pelrun/cpc-schematics/docs/new-fcu.png

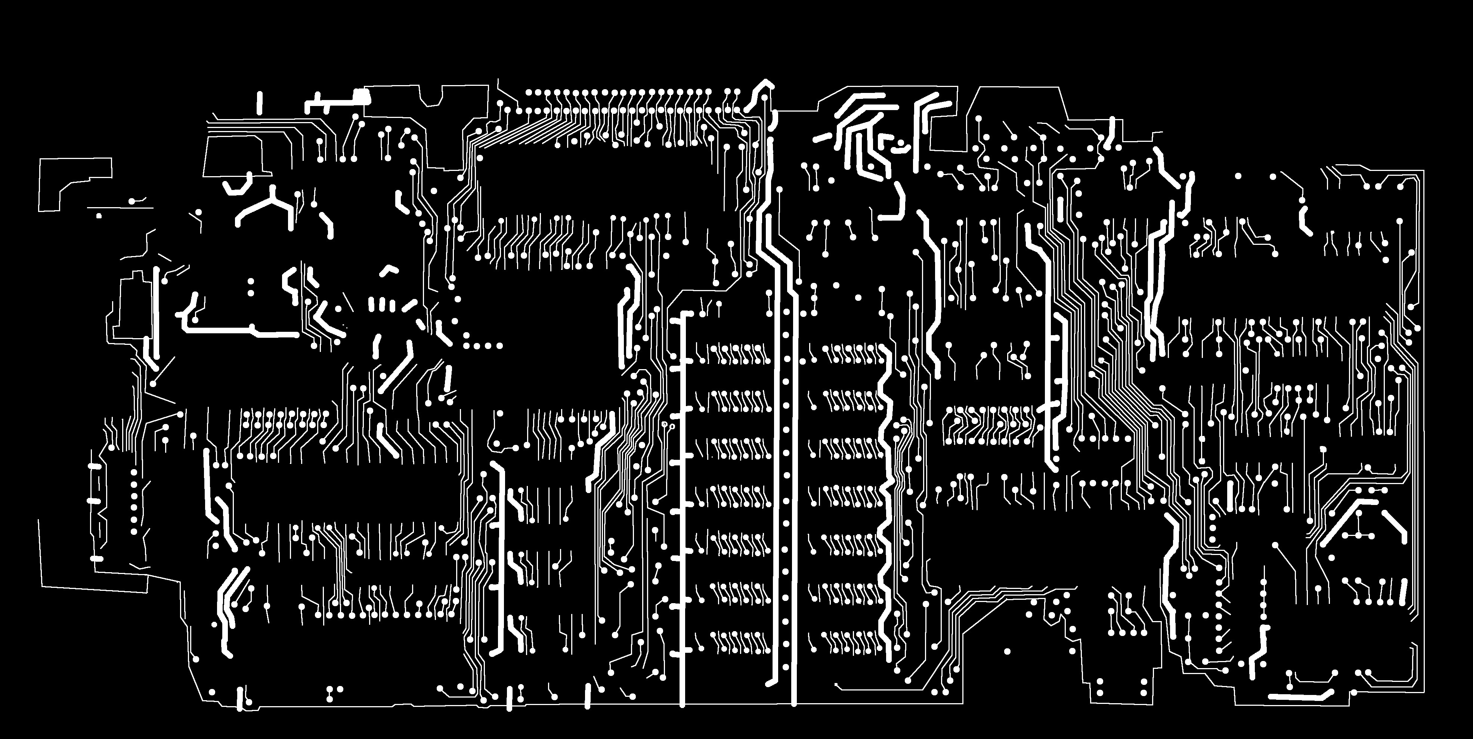
docs/new-fcu.png
