pelrun/cpc-schematics/cpc6128/disc-ver2.kicad_sch

## KiCad design cpc6128/disc-ver2.kicad_sch (2025-07-12)

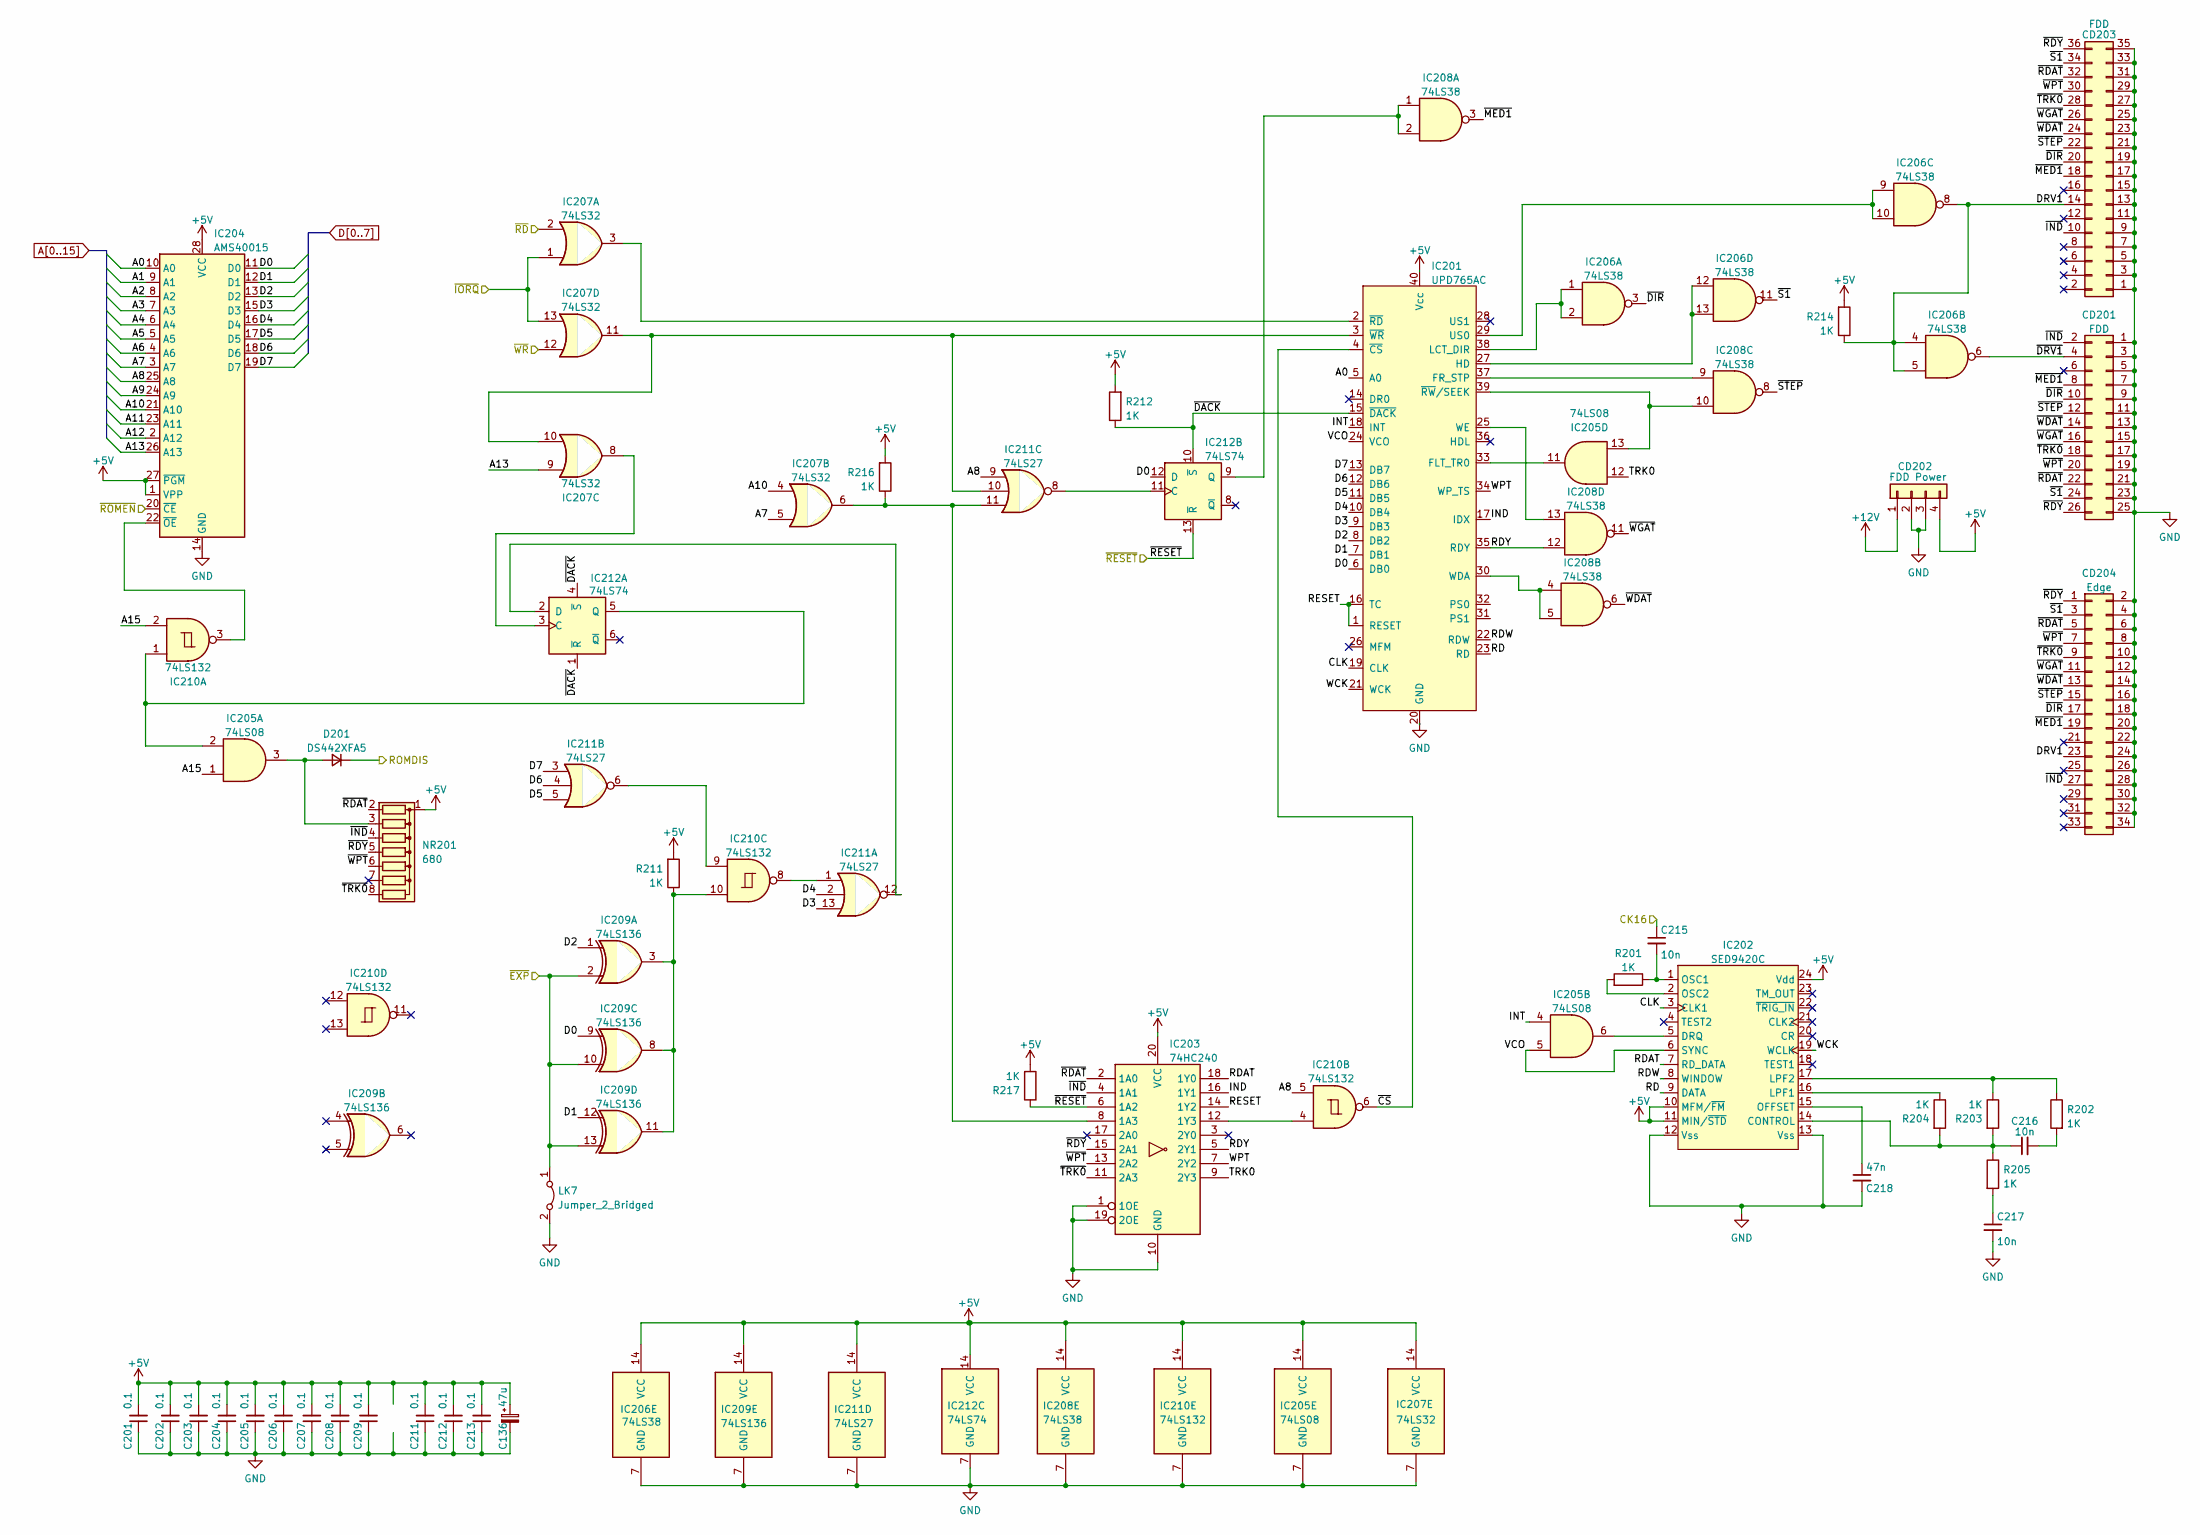
[picture p20: schematic disc-ver2.kicad_sch]

Parts:
C136: 47u; CP_Radial_D4.0mm_P5.00mm
C201, C202, C203, C204, C205, C206, C207, C208, C209, C211, C212, C213: 0.1; C_Disc_D4.3mm_W1.9mm_P5.00mm
C215, C216, C217: 10n; C_Rect_L7.0mm_W2.0mm_P5.00mm
C218: 47n; C_Rect_L7.0mm_W2.0mm_P5.00mm
CD201: FDD; IDC-Header_2x13_P2.54mm_Vertical
CD202: FDD Power; FDD_Power
CD203: FDD; 36-PIN-CENTRONICS
CD204: Edge; Edge_Conn_2x17
D201: DS442XFA5; D_DO-35_SOD27_P10.16mm_Horizontal
IC201: UPD765AC; DIP-40_W15.24mm
IC202: SED9420C; DIP-24_W15.24mm
IC203: 74HC240; DIP-20_W7.62mm
IC204: AMS40015; DIP-28_W15.24mm
IC205: 74LS08; DIP-14_W7.62mm
IC206, IC208: 74LS38; DIP-14_W7.62mm
IC207: 74LS32; DIP-14_W7.62mm
IC209: 74LS136; DIP-14_W7.62mm
IC210: 74LS132; DIP-14_W7.62mm
IC211: 74LS27; DIP-14_W7.62mm
IC212: 74LS74; DIP-14_W7.62mm
LK7: Jumper_2_Bridged; LINK
NR201: 680; R_Array_SIP8
R201, R202, R203, R204, R205, R211, R212, R214, R216, R217: 1K; R_Axial_DIN0207_L6.3mm_D2.5mm_P10.16mm_Horizontal

Connections:
+5V: C136.1, C201.2, C202.2, C203.2, C204.2, C205.2, C206.2, C207.2, C208.2, C209.2, C211.2, C212.2, C213.2, CD202.4, IC201.40 (Vcc), IC202.10 (MFM/~FM), IC202.11 (MIN/~STD), IC202.24 (Vdd), IC203.20 (VCC), IC204.1 (VPP), IC204.27 (~PGM), IC204.28 (VCC), IC205.14 (VCC), IC206.14 (VCC), IC207.14 (VCC), IC208.14 (VCC), IC209.14 (VCC), IC210.14 (VCC), IC211.14 (VCC), IC212.14 (VCC), NR201.1 (common), R211.2, R212.2, R214.2, R216.2, R217.2
+12V: CD202.1
A0: IC201.5 (A0), IC204.10 (A0)
A1: IC204.9 (A1)
A2: IC204.8 (A2)
A3: IC204.7 (A3)
A4: IC204.6 (A4)
A5: IC204.5 (A5)
A6: IC204.4 (A6)
A7: IC204.3 (A7), IC207.5
A8: IC204.25 (A8), IC210.5, IC211.9
A9: IC204.24 (A9)
A10: IC204.21 (A10), IC207.4
A11: IC204.23 (A11)
A12: IC204.2 (A12)
A13: IC204.26 (A13), IC207.9
A15: IC205.1, IC210.2
CK16: C215.1
CLK: IC201.19 (CLK), IC202.3 (CLK1)
D0: IC201.6 (DB0), IC204.11 (D0), IC209.9, IC212.12 (D)
D1: IC201.7 (DB1), IC204.12 (D1), IC209.12
D2: IC201.8 (DB2), IC204.13 (D2), IC209.1
D3: IC201.9 (DB3), IC204.15 (D3), IC211.13
D4: IC201.10 (DB4), IC204.16 (D4), IC211.2
D5: IC201.11 (DB5), IC204.17 (D5), IC211.5
D6: IC201.12 (DB6), IC204.18 (D6), IC211.4
D7: IC201.13 (DB7), IC204.19 (D7), IC211.3
DRV1: CD203.14, CD204.23, IC206.4, IC206.5, IC206.8, R214.1
GND: C136.2, C201.1, C202.1, C203.1, C204.1, C205.1, C206.1, C207.1, C208.1, C209.1, C211.1, C212.1, C213.1, C217.2, C218.2, CD201.1, CD201.3, CD201.5, CD201.7, CD201.9, CD201.11, CD201.13, CD201.15, CD201.17, CD201.19, CD201.21, CD201.23, CD201.25, CD202.2, CD202.3, CD203.1, CD203.3, CD203.5, CD203.7, CD203.9, CD203.11, CD203.13, CD203.15, CD203.17, CD203.19, CD203.21, CD203.23, CD203.25, CD203.27, CD203.29, CD203.31, CD203.33, CD203.35, CD204.2, CD204.4, CD204.6, CD204.8, CD204.10, CD204.12, CD204.14, CD204.16, CD204.18, CD204.20, CD204.22, CD204.24, CD204.26, CD204.28, CD204.30, CD204.32, CD204.34, IC201.20 (GND), IC202.12 (Vss), IC202.13 (Vss), IC203.1 (1OE), IC203.10 (GND), IC203.19 (2OE), IC204.14 (GND), IC205.7 (GND), IC206.7 (GND), IC207.7 (GND), IC208.7 (GND), IC209.7 (GND), IC210.7 (GND), IC211.7 (GND), IC212.7 (GND), LK7.2 (B)
IND: IC201.17 (IDX), IC203.16 (1Y1)
INT: IC201.18 (INT), IC205.4
unnamed: C215.2, IC202.1 (OSC1), R201.1
unnamed: C216.1, IC202.14 (CONTROL), R203.2, R204.2, R205.1
unnamed: C216.2, R202.2
unnamed: C217.1, R205.2
unnamed: C218.1, IC202.15 (OFFSET)
unnamed: D201.2 (A), IC205.3, NR201.3 (R2)
unnamed: IC201.2 (~RD), IC207.3
unnamed: IC201.3 (~WR), IC207.10, IC207.11, IC211.10
unnamed: IC201.25 (WE), IC208.13
unnamed: IC201.27 (HD), IC206.12, IC206.13
unnamed: IC201.29 (US0), IC206.9, IC206.10
unnamed: IC201.30 (WDA), IC208.4, IC208.5
unnamed: IC201.33 (FLT_TR0), IC205.11
unnamed: IC201.37 (FR_STP), IC208.9
unnamed: IC201.38 (LCT_DIR), IC206.1, IC206.2
unnamed: IC201.39 (~RW/SEEK), IC205.13, IC208.10
unnamed: IC202.2 (OSC2), R201.2
unnamed: IC202.5 (DRQ), IC205.6
unnamed: IC202.16 (LPF1), R204.1
unnamed: IC202.17 (LPF2), R202.1, R203.1
unnamed: IC203.8 (1A3), IC207.6, IC211.11, R216.1
unnamed: IC203.12 (1Y3), IC210.4
unnamed: IC204.22 (~OE), IC210.3
unnamed: IC205.2, IC210.1, IC212.5 (Q)
unnamed: IC207.8, IC212.3 (C)
unnamed: IC208.1, IC208.2, IC212.9 (Q)
unnamed: IC209.3, IC209.8, IC209.11, IC210.10, R211.1
unnamed: IC210.8, IC211.1
unnamed: IC210.9, IC211.6
unnamed: IC211.8, IC212.11 (C)
unnamed: IC211.12, IC212.2 (D)
RD: IC201.23 (RD), IC202.9 (DATA)
RDAT: IC202.7 (RD_DATA), IC203.18 (1Y0)
RDW: IC201.22 (RDW), IC202.8 (WINDOW)
RDY: IC201.35 (RDY), IC203.5 (2Y1), IC208.12
RESET: IC201.1 (RESET), IC201.16 (TC), IC203.14 (1Y2)
ROMDIS: D201.1 (K)
TRK0: IC203.9 (2Y3), IC205.12
VCO: IC201.24 (VCO), IC202.6 (SYNC), IC205.5
WCK: IC201.21 (WCK), IC202.19 (WCLK)
WPT: IC201.34 (WP_TS), IC203.7 (2Y2)
~CS: IC201.4 (~CS), IC210.6
~DACK: IC201.15 (~DACK), IC212.1 (~R), IC212.4 (~S), IC212.10 (~S), R212.1
~DIR: CD201.10, CD203.20, CD204.17, IC206.3
~DRV1: CD201.4, IC206.6
~EXP: IC209.2, IC209.10, IC209.13, LK7.1 (A)
~IND: CD201.2, CD203.10, CD204.27, IC203.4 (1A1), NR201.4 (R3)
~IORQ: IC207.1, IC207.13
~MED1: CD201.8, CD203.18, CD204.19, IC208.3
~RDAT: CD201.22, CD203.32, CD204.5, IC203.2 (1A0), NR201.2 (R1)
~RDY: CD201.26, CD203.36, CD204.1, IC203.15 (2A1), NR201.5 (R4)
~RD: IC207.2
~RESET: IC203.6 (1A2), IC212.13 (~R), R217.1
~ROMEN: IC204.20 (~CE)
~S1: CD201.24, CD203.34, CD204.3, IC206.11
~STEP: CD201.12, CD203.22, CD204.15, IC208.8
~TRK0: CD201.18, CD203.28, CD204.9, IC203.11 (2A3), NR201.8 (R7)
~WDAT: CD201.14, CD203.24, CD204.13, IC208.6
~WGAT: CD201.16, CD203.26, CD204.11, IC208.11
~WPT: CD201.20, CD203.30, CD204.7, IC203.13 (2A2), NR201.6 (R5)
~WR: IC207.12
