pelrun/cpc-schematics/cpc6128/mc0020x.kicad_sch

## KiCad design cpc6128/mc0020x.kicad_sch (2025-07-12)

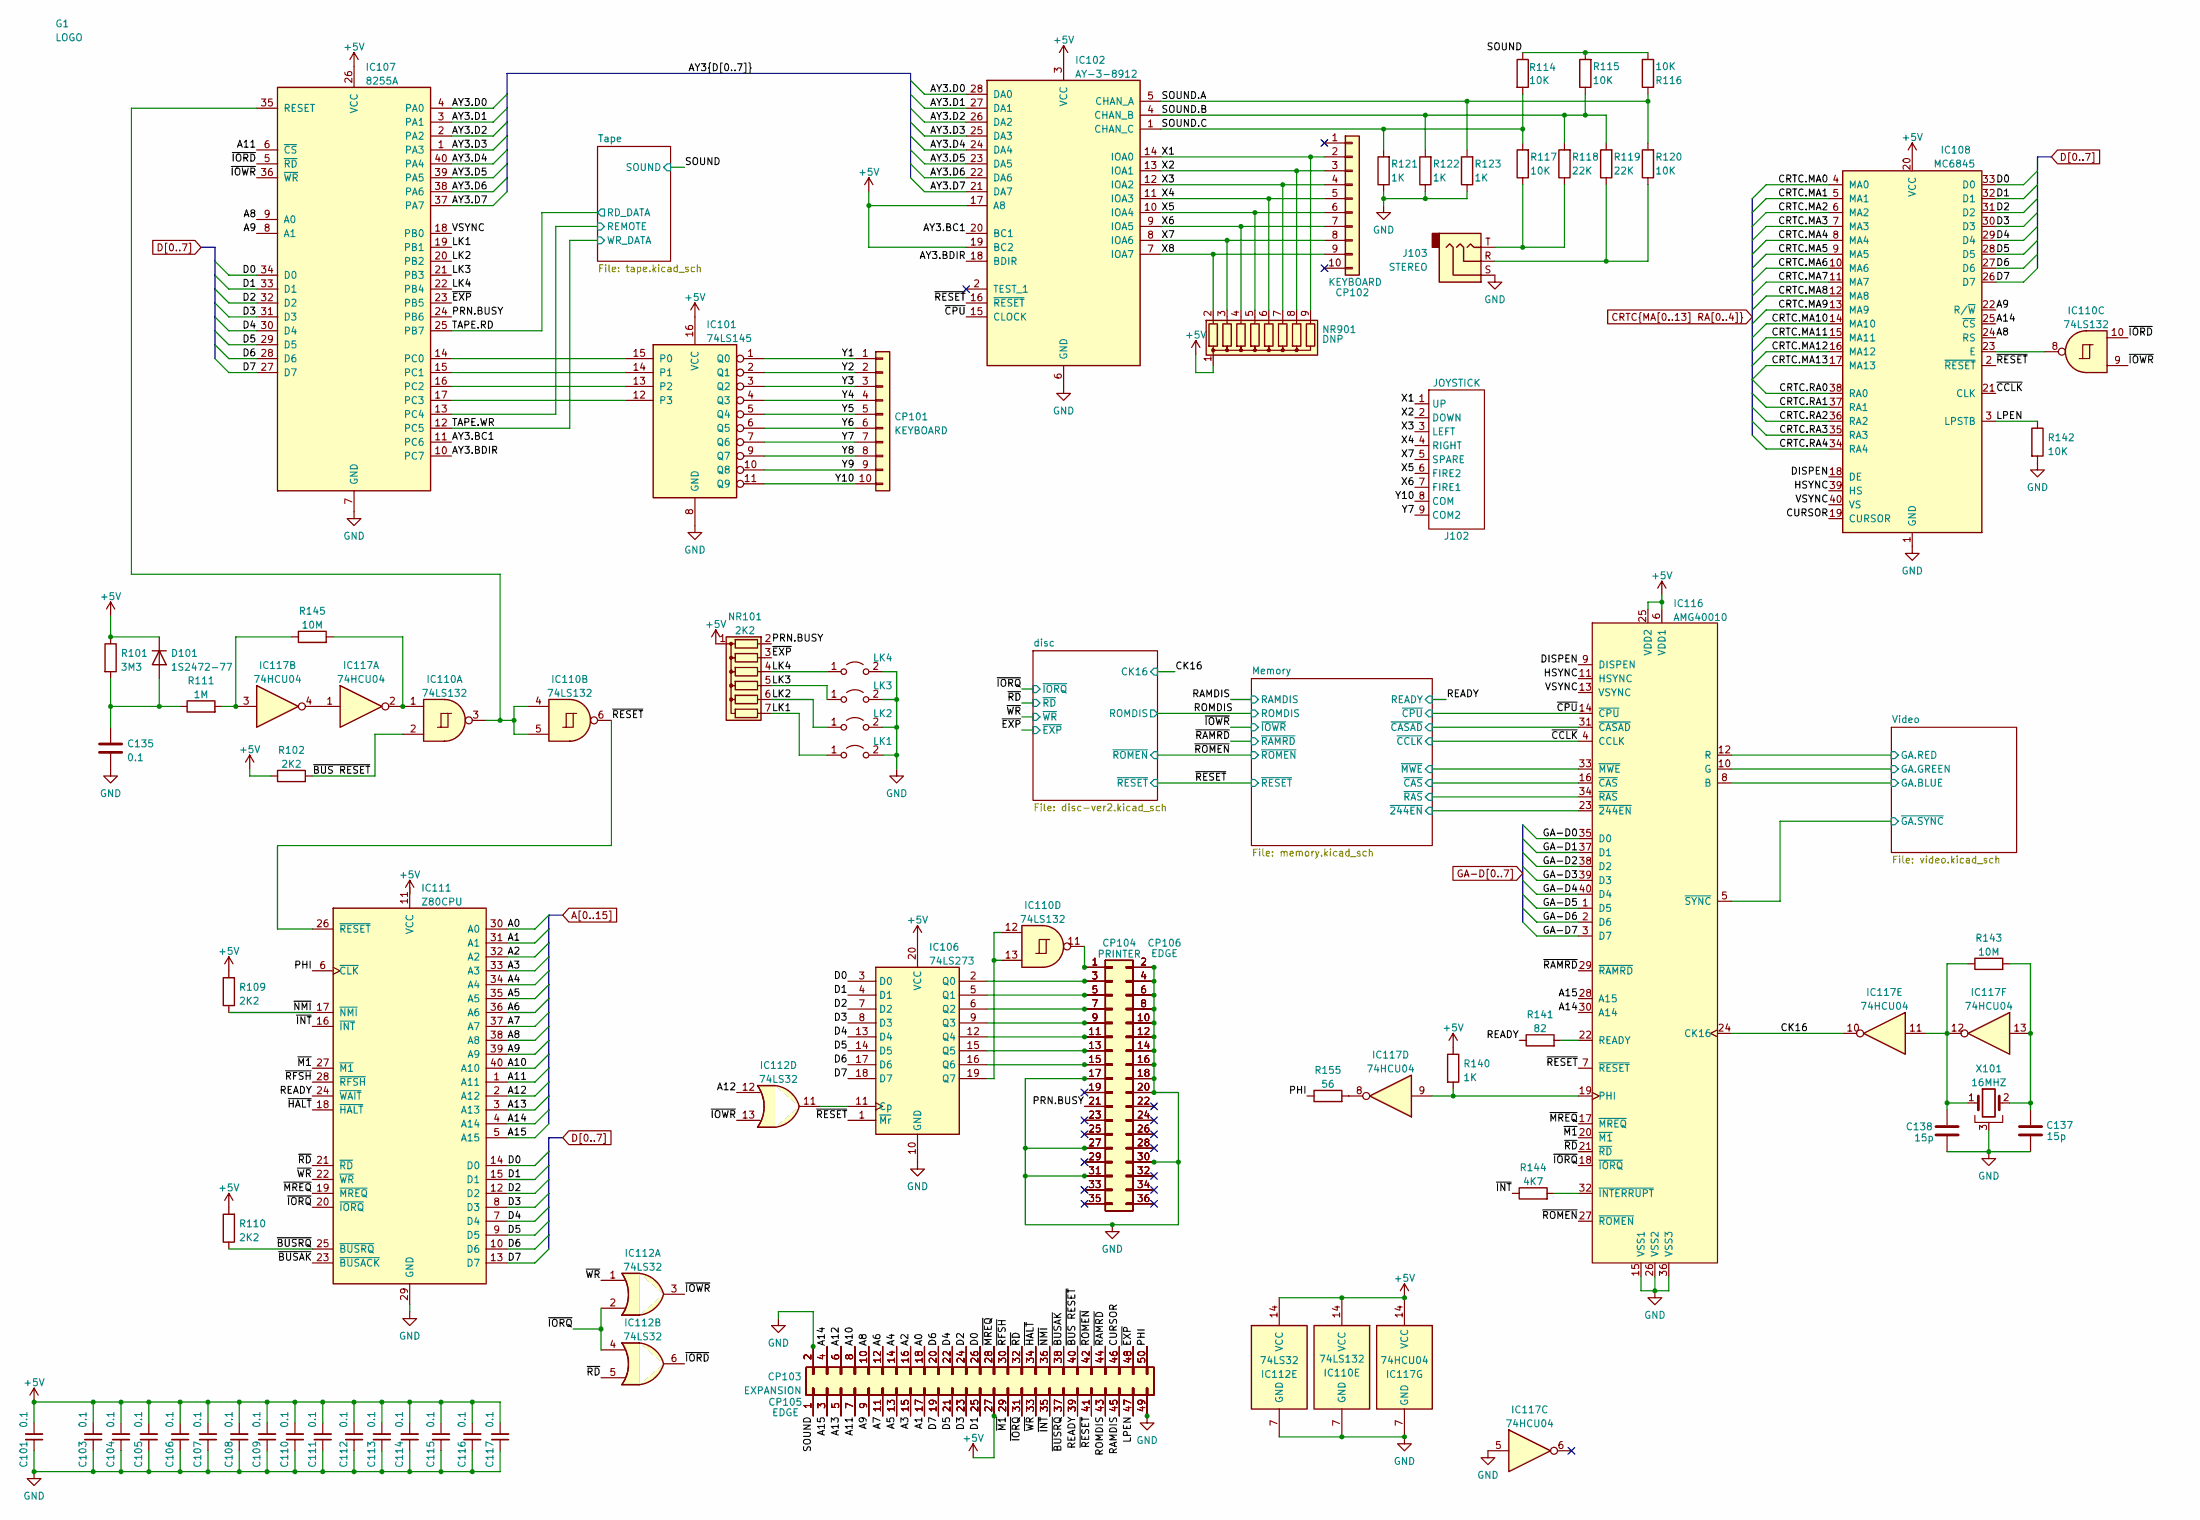
[picture p21: schematic mc0020x.kicad_sch]

Parts:
C101, C103, C104, C105, C106, C107, C108, C109, C110, C111, C112, C113, C114, C115, C116, C117, C135: 0.1; C_Disc_D4.3mm_W1.9mm_P5.00mm
C137, C138: 15p; C_Disc_D4.3mm_W1.9mm_P5.00mm
CP101, CP102: KEYBOARD; HBLB10S-5J
CP103: EXPANSION; 50-PIN-CENTRONICS
CP104: PRINTER; 36-PIN-CENTRONICS
CP105: EDGE; Edge_Conn_2x25
CP106: EDGE; Edge_Conn_2x17
D101: 1S2472-77; D_DO-35_SOD27_P10.16mm_Horizontal
G1: LOGO
IC101: 74LS145; DIP-16_W7.62mm
IC102: AY-3-8912; DIP-28_W15.24mm
IC106: 74LS273; DIP-20_W7.62mm
IC107: 8255A; DIP-40_W15.24mm
IC108: MC6845; DIP-40_W15.24mm
IC110: 74LS132; DIP-14_W7.62mm
IC111: Z80CPU; DIP-40_W15.24mm
IC112: 74LS32; DIP-14_W7.62mm
IC116: AMG40010; DIP-40_W15.24mm_Socket
IC117: 74HCU04; DIP-14_W7.62mm
J102: JOYSTICK; DSUB-9_Male_Horizontal_P2.77x2.54mm_EdgePinOffset9.40mm
J103: STEREO; HSJ1061-0104409
LK1, LK2, LK3, LK4: Jumper_2_Open; LINK
NR101: 2K2; R_Array_SIP7
NR901: DNP; R_Array_SIP9
R101: 3M3; R_Axial_DIN0207_L6.3mm_D2.5mm_P10.16mm_Horizontal
R102, R109, R110: 2K2; R_Axial_DIN0207_L6.3mm_D2.5mm_P10.16mm_Horizontal
R111: 1M; R_Axial_DIN0207_L6.3mm_D2.5mm_P10.16mm_Horizontal
R114, R115, R116, R117, R120, R142: 10K; R_Axial_DIN0207_L6.3mm_D2.5mm_P10.16mm_Horizontal
R118, R119: 22K; R_Axial_DIN0207_L6.3mm_D2.5mm_P10.16mm_Horizontal
R121, R122, R123, R140: 1K; R_Axial_DIN0207_L6.3mm_D2.5mm_P10.16mm_Horizontal
R141: 82; R_Axial_DIN0207_L6.3mm_D2.5mm_P10.16mm_Horizontal
R143, R145: 10M; R_Axial_DIN0207_L6.3mm_D2.5mm_P10.16mm_Horizontal
R144: 4K7; R_Axial_DIN0207_L6.3mm_D2.5mm_P10.16mm_Horizontal
R155: 56; R_Axial_DIN0207_L6.3mm_D2.5mm_P10.16mm_Horizontal
X101: 16MHZ; Crystal_HC18-U_Horizontal_1EP_style1

Connections:
+5V: C101.2, C103.2, C104.2, C105.2, C106.2, C107.2, C108.2, C109.2, C110.2, C111.2, C112.2, C113.2, C114.2, C115.2, C116.2, C117.2, CP103.27, CP105.27, D101.1 (K), IC101.16 (VCC), IC102.3 (VCC), IC102.17 (A8), IC102.19 (BC2), IC106.20 (VCC), IC107.26 (VCC), IC108.20 (VCC), IC110.14 (VCC), IC111.11 (VCC), IC112.14 (VCC), IC116.6 (VDD1), IC116.25 (VDD2), IC117.14 (VCC), NR101.1 (common), NR901.1 (common), R101.1, R102.1, R109.2, R110.2, R140.1
A0: CP103.18, CP105.18, IC111.30 (A0)
A1: CP103.17, CP105.17, IC111.31 (A1)
A2: CP103.16, CP105.16, IC111.32 (A2)
A3: CP103.15, CP105.15, IC111.33 (A3)
A4: CP103.14, CP105.14, IC111.34 (A4)
A5: CP103.13, CP105.13, IC111.35 (A5)
A6: CP103.12, CP105.12, IC111.36 (A6)
A7: CP103.11, CP105.11, IC111.37 (A7)
A8: CP103.10, CP105.10, IC107.9 (A0), IC108.24 (RS), IC111.38 (A8)
A9: CP103.9, CP105.9, IC107.8 (A1), IC108.22 (R/~W), IC111.39 (A9)
A10: CP103.8, CP105.8, IC111.40 (A10)
A11: CP103.7, CP105.7, IC107.6 (~CS), IC111.1 (A11)
A12: CP103.6, CP105.6, IC111.2 (A12), IC112.12
A13: CP103.5, CP105.5, IC111.3 (A13)
A14: CP103.4, CP105.4, IC108.25 (~CS), IC111.4 (A14), IC116.30 (A14)
A15: CP103.3, CP105.3, IC111.5 (A15), IC116.28 (A15)
AY3.BC1: IC102.20 (BC1), IC107.11 (PC6)
AY3.BDIR: IC102.18 (BDIR), IC107.10 (PC7)
AY3.D0: IC102.28 (DA0), IC107.4 (PA0)
AY3.D1: IC102.27 (DA1), IC107.3 (PA1)
AY3.D2: IC102.26 (DA2), IC107.2 (PA2)
AY3.D3: IC102.25 (DA3), IC107.1 (PA3)
AY3.D4: IC102.24 (DA4), IC107.40 (PA4)
AY3.D5: IC102.23 (DA5), IC107.39 (PA5)
AY3.D6: IC102.22 (DA6), IC107.38 (PA6)
AY3.D7: IC102.21 (DA7), IC107.37 (PA7)
CK16: IC116.24 (CK16), IC117.10
CRTC.MA0: IC108.4 (MA0)
CRTC.MA1: IC108.5 (MA1)
CRTC.MA2: IC108.6 (MA2)
CRTC.MA3: IC108.7 (MA3)
CRTC.MA4: IC108.8 (MA4)
CRTC.MA5: IC108.9 (MA5)
CRTC.MA6: IC108.10 (MA6)
CRTC.MA7: IC108.11 (MA7)
CRTC.MA8: IC108.12 (MA8)
CRTC.MA9: IC108.13 (MA9)
CRTC.MA10: IC108.14 (MA10)
CRTC.MA11: IC108.15 (MA11)
CRTC.MA12: IC108.16 (MA12)
CRTC.MA13: IC108.17 (MA13)
CRTC.RA0: IC108.38 (RA0)
CRTC.RA1: IC108.37 (RA1)
CRTC.RA2: IC108.36 (RA2)
CRTC.RA3: IC108.35 (RA3)
CRTC.RA4: IC108.34 (RA4)
CURSOR: CP103.46, CP105.46, IC108.19 (CURSOR)
D0: CP103.26, CP105.26, IC106.3 (D0), IC107.34 (D0), IC108.33 (D0), IC111.14 (D0)
D1: CP103.25, CP105.25, IC106.4 (D1), IC107.33 (D1), IC108.32 (D1), IC111.15 (D1)
D2: CP103.24, CP105.24, IC106.7 (D2), IC107.32 (D2), IC108.31 (D2), IC111.12 (D2)
D3: CP103.23, CP105.23, IC106.8 (D3), IC107.31 (D3), IC108.30 (D3), IC111.8 (D3)
D4: CP103.22, CP105.22, IC106.13 (D4), IC107.30 (D4), IC108.29 (D4), IC111.7 (D4)
D5: CP103.21, CP105.21, IC106.14 (D5), IC107.29 (D5), IC108.28 (D5), IC111.9 (D5)
D6: CP103.20, CP105.20, IC106.17 (D6), IC107.28 (D6), IC108.27 (D6), IC111.10 (D6)
D7: CP103.19, CP105.19, IC106.18 (D7), IC107.27 (D7), IC108.26 (D7), IC111.13 (D7)
DISPEN: IC108.18 (DE), IC116.9 (DISPEN)
GA-D0: IC116.35 (D0)
GA-D1: IC116.37 (D1)
GA-D2: IC116.38 (D2)
GA-D3: IC116.39 (D3)
GA-D4: IC116.40 (D4)
GA-D5: IC116.1 (D5)
GA-D6: IC116.2 (D6)
GA-D7: IC116.3 (D7)
GA.BLUE: IC116.8 (B)
GA.GREEN: IC116.10 (G)
GA.RED: IC116.12 (R)
GND: C101.1, C103.1, C104.1, C105.1, C106.1, C107.1, C108.1, C109.1, C110.1, C111.1, C112.1, C113.1, C114.1, C115.1, C116.1, C117.1, C135.2, C137.1, C138.2, CP103.2, CP103.49, CP104.2, CP104.4, CP104.6, CP104.8, CP104.10, CP104.12, CP104.14, CP104.16, CP104.17, CP104.18, CP104.20, CP104.27, CP104.30, CP104.31, CP105.2, CP105.49, CP106.2, CP106.4, CP106.6, CP106.8, CP106.10, CP106.12, CP106.14, CP106.16, CP106.17, CP106.18, CP106.20, CP106.27, CP106.30, CP106.31, IC101.8 (GND), IC102.6 (GND), IC106.10 (GND), IC107.7 (GND), IC108.1 (GND), IC110.7 (GND), IC111.29 (GND), IC112.7 (GND), IC116.15 (VSS1), IC116.26 (VSS2), IC116.36 (VSS3), IC117.5, IC117.7 (GND), J103.S, LK1.2 (B), LK2.2 (B), LK3.2 (B), LK4.2 (B), R121.1, R122.1, R123.1, R142.2, X101.3
HSYNC: IC108.39 (HS), IC116.11 (HSYNC)
LK1: IC107.19 (PB1), LK1.1 (A), NR101.7 (R6)
LK2: IC107.20 (PB2), LK2.1 (A), NR101.6 (R5)
LK3: IC107.21 (PB3), LK3.1 (A), NR101.5 (R4)
LK4: IC107.22 (PB4), LK4.1 (A), NR101.4 (R3)
LPEN: CP103.47, CP105.47, IC108.3 (LPSTB), R142.1
unnamed: C135.1, D101.2 (A), R101.2, R111.1
unnamed: C137.2, IC117.13, R143.2, X101.2
unnamed: C138.1, IC117.11, IC117.12, R143.1, X101.1
unnamed: CP104.1, CP106.1, IC110.11
unnamed: CP104.3, CP106.3, IC106.2 (Q0)
unnamed: CP104.5, CP106.5, IC106.5 (Q1)
unnamed: CP104.7, CP106.7, IC106.6 (Q2)
unnamed: CP104.9, CP106.9, IC106.9 (Q3)
unnamed: CP104.11, CP106.11, IC106.12 (Q4)
unnamed: CP104.13, CP106.13, IC106.15 (Q5)
unnamed: CP104.15, CP106.15, IC106.16 (Q6)
unnamed: CP104.19, CP106.19
unnamed: CP104.22, CP106.22
unnamed: CP104.23, CP106.23
unnamed: CP104.24, CP106.24
unnamed: CP104.25, CP106.25
unnamed: CP104.26, CP106.26
unnamed: CP104.28, CP106.28
unnamed: CP104.29, CP106.29
unnamed: CP104.32, CP106.32
unnamed: CP104.33, CP106.33
unnamed: CP104.34, CP106.34
unnamed: CP104.35, CP106.35
unnamed: CP104.36, CP106.36
unnamed: IC101.12 (P3), IC107.17 (PC3)
unnamed: IC101.13 (P2), IC107.16 (PC2)
unnamed: IC101.14 (P1), IC107.15 (PC1)
unnamed: IC101.15 (P0), IC107.14 (PC0)
unnamed: IC106.11 (Cp), IC112.11
unnamed: IC106.19 (Q7), IC110.12, IC110.13
unnamed: IC107.35 (RESET), IC110.3, IC110.4, IC110.5
unnamed: IC108.23 (E), IC110.8
unnamed: IC110.1, IC117.2, R145.2
unnamed: IC116.19 (PHI), IC117.9, R140.2
unnamed: IC116.22 (READY), R141.2
unnamed: IC116.32 (~INTERRUPT), R144.2
unnamed: IC117.1, IC117.4
unnamed: IC117.3, R111.2, R145.1
unnamed: IC117.8, R155.2
unnamed: J103.R, R119.1, R120.1
unnamed: J103.T, R117.1, R118.1
PHI: CP103.50, CP105.50, IC111.6 (~CLK), R155.1
PRN.BUSY: CP104.21, CP106.21, IC107.24 (PB6), NR101.2 (R1)
RAMDIS: CP103.45, CP105.45
READY: CP103.39, CP105.39, IC111.24 (~WAIT), R141.1
REMOTE: IC107.13 (PC4)
ROMDIS: CP103.43, CP105.43
SOUND: CP103.1, CP105.1, R114.1, R115.2, R116.1
SOUND.A: IC102.5 (CHAN_A), R116.2, R120.2, R123.2
SOUND.B: IC102.4 (CHAN_B), R115.1, R118.2, R119.2, R122.2
SOUND.C: IC102.1 (CHAN_C), R114.2, R117.2, R121.2
TAPE.RD: IC107.25 (PB7)
TAPE.WR: IC107.12 (PC5)
VSYNC: IC107.18 (PB0), IC108.40 (VS), IC116.13 (VSYNC)
X1: CP102.2, IC102.14 (IOA0), J102.1 (UP), NR901.9 (R8)
X2: CP102.3, IC102.13 (IOA1), J102.2 (DOWN), NR901.8 (R7)
X3: CP102.4, IC102.12 (IOA2), J102.3 (LEFT), NR901.7 (R6)
X4: CP102.5, IC102.11 (IOA3), J102.4 (RIGHT), NR901.6 (R5)
X5: CP102.6, IC102.10 (IOA4), J102.6 (FIRE2), NR901.5 (R4)
X6: CP102.7, IC102.9 (IOA5), J102.7 (FIRE1), NR901.4 (R3)
X7: CP102.8, IC102.8 (IOA6), J102.5 (SPARE), NR901.3 (R2)
X8: CP102.9, IC102.7 (IOA7), NR901.2 (R1)
Y1: CP101.1, IC101.1 (Q0)
Y2: CP101.2, IC101.2 (Q1)
Y3: CP101.3, IC101.3 (Q2)
Y4: CP101.4, IC101.4 (Q3)
Y5: CP101.5, IC101.5 (Q4)
Y6: CP101.6, IC101.6 (Q5)
Y7: CP101.7, IC101.7 (Q6), J102.9 (COM2)
Y8: CP101.8, IC101.9 (Q7)
Y9: CP101.9, IC101.10 (Q8)
Y10: CP101.10, IC101.11 (Q9), J102.8 (COM)
~244EN: IC116.23 (~244EN)
~BUS RESET: CP103.40, CP105.40, IC110.2, R102.2
~BUSAK: CP103.38, CP105.38, IC111.23 (~BUSACK)
~BUSRQ: CP103.37, CP105.37, IC111.25 (~BUSRQ), R110.1
~CASAD: IC116.31 (~CASAD)
~CAS: IC116.16 (~CAS)
~CCLK: IC108.21 (CLK), IC116.4 (CCLK)
~CPU: IC102.15 (CLOCK), IC116.14 (~CPU)
~EXP: CP103.48, CP105.48, IC107.23 (PB5), NR101.3 (R2)
~GA.SYNC: IC116.5 (~SYNC)
~HALT: CP103.34, CP105.34, IC111.18 (~HALT)
~INT: CP103.35, CP105.35, IC111.16 (~INT), R144.1
~IORD: IC107.5 (~RD), IC110.10, IC112.6
~IORQ: CP103.31, CP105.31, IC111.20 (~IORQ), IC112.2, IC112.4, IC116.18 (~IORQ)
~IOWR: IC107.36 (~WR), IC110.9, IC112.3, IC112.13
~M1: CP103.29, CP105.29, IC111.27 (~M1), IC116.20 (~M1)
~MREQ: CP103.28, CP105.28, IC111.19 (~MREQ), IC116.17 (~MREQ)
~MWE: IC116.33 (~MWE)
~NMI: CP103.36, CP105.36, IC111.17 (~NMI), R109.1
~RAMRD: CP103.44, CP105.44, IC116.29 (~RAMRD)
~RAS: IC116.34 (~RAS)
~RD: CP103.32, CP105.32, IC111.21 (~RD), IC112.5, IC116.21 (~RD)
~RESET: CP103.41, CP105.41, IC102.16 (~RESET), IC106.1 (~Mr), IC108.2 (~RESET), IC110.6, IC111.26 (~RESET), IC116.7 (~RESET)
~RFSH: CP103.30, CP105.30, IC111.28 (~RFSH)
~ROMEN: CP103.42, CP105.42, IC116.27 (~ROMEN)
~WR: CP103.33, CP105.33, IC111.22 (~WR), IC112.1
