pelrun/cpc-schematics/cpc6128/memory.kicad_sch

## KiCad design cpc6128/memory.kicad_sch (2025-07-12)

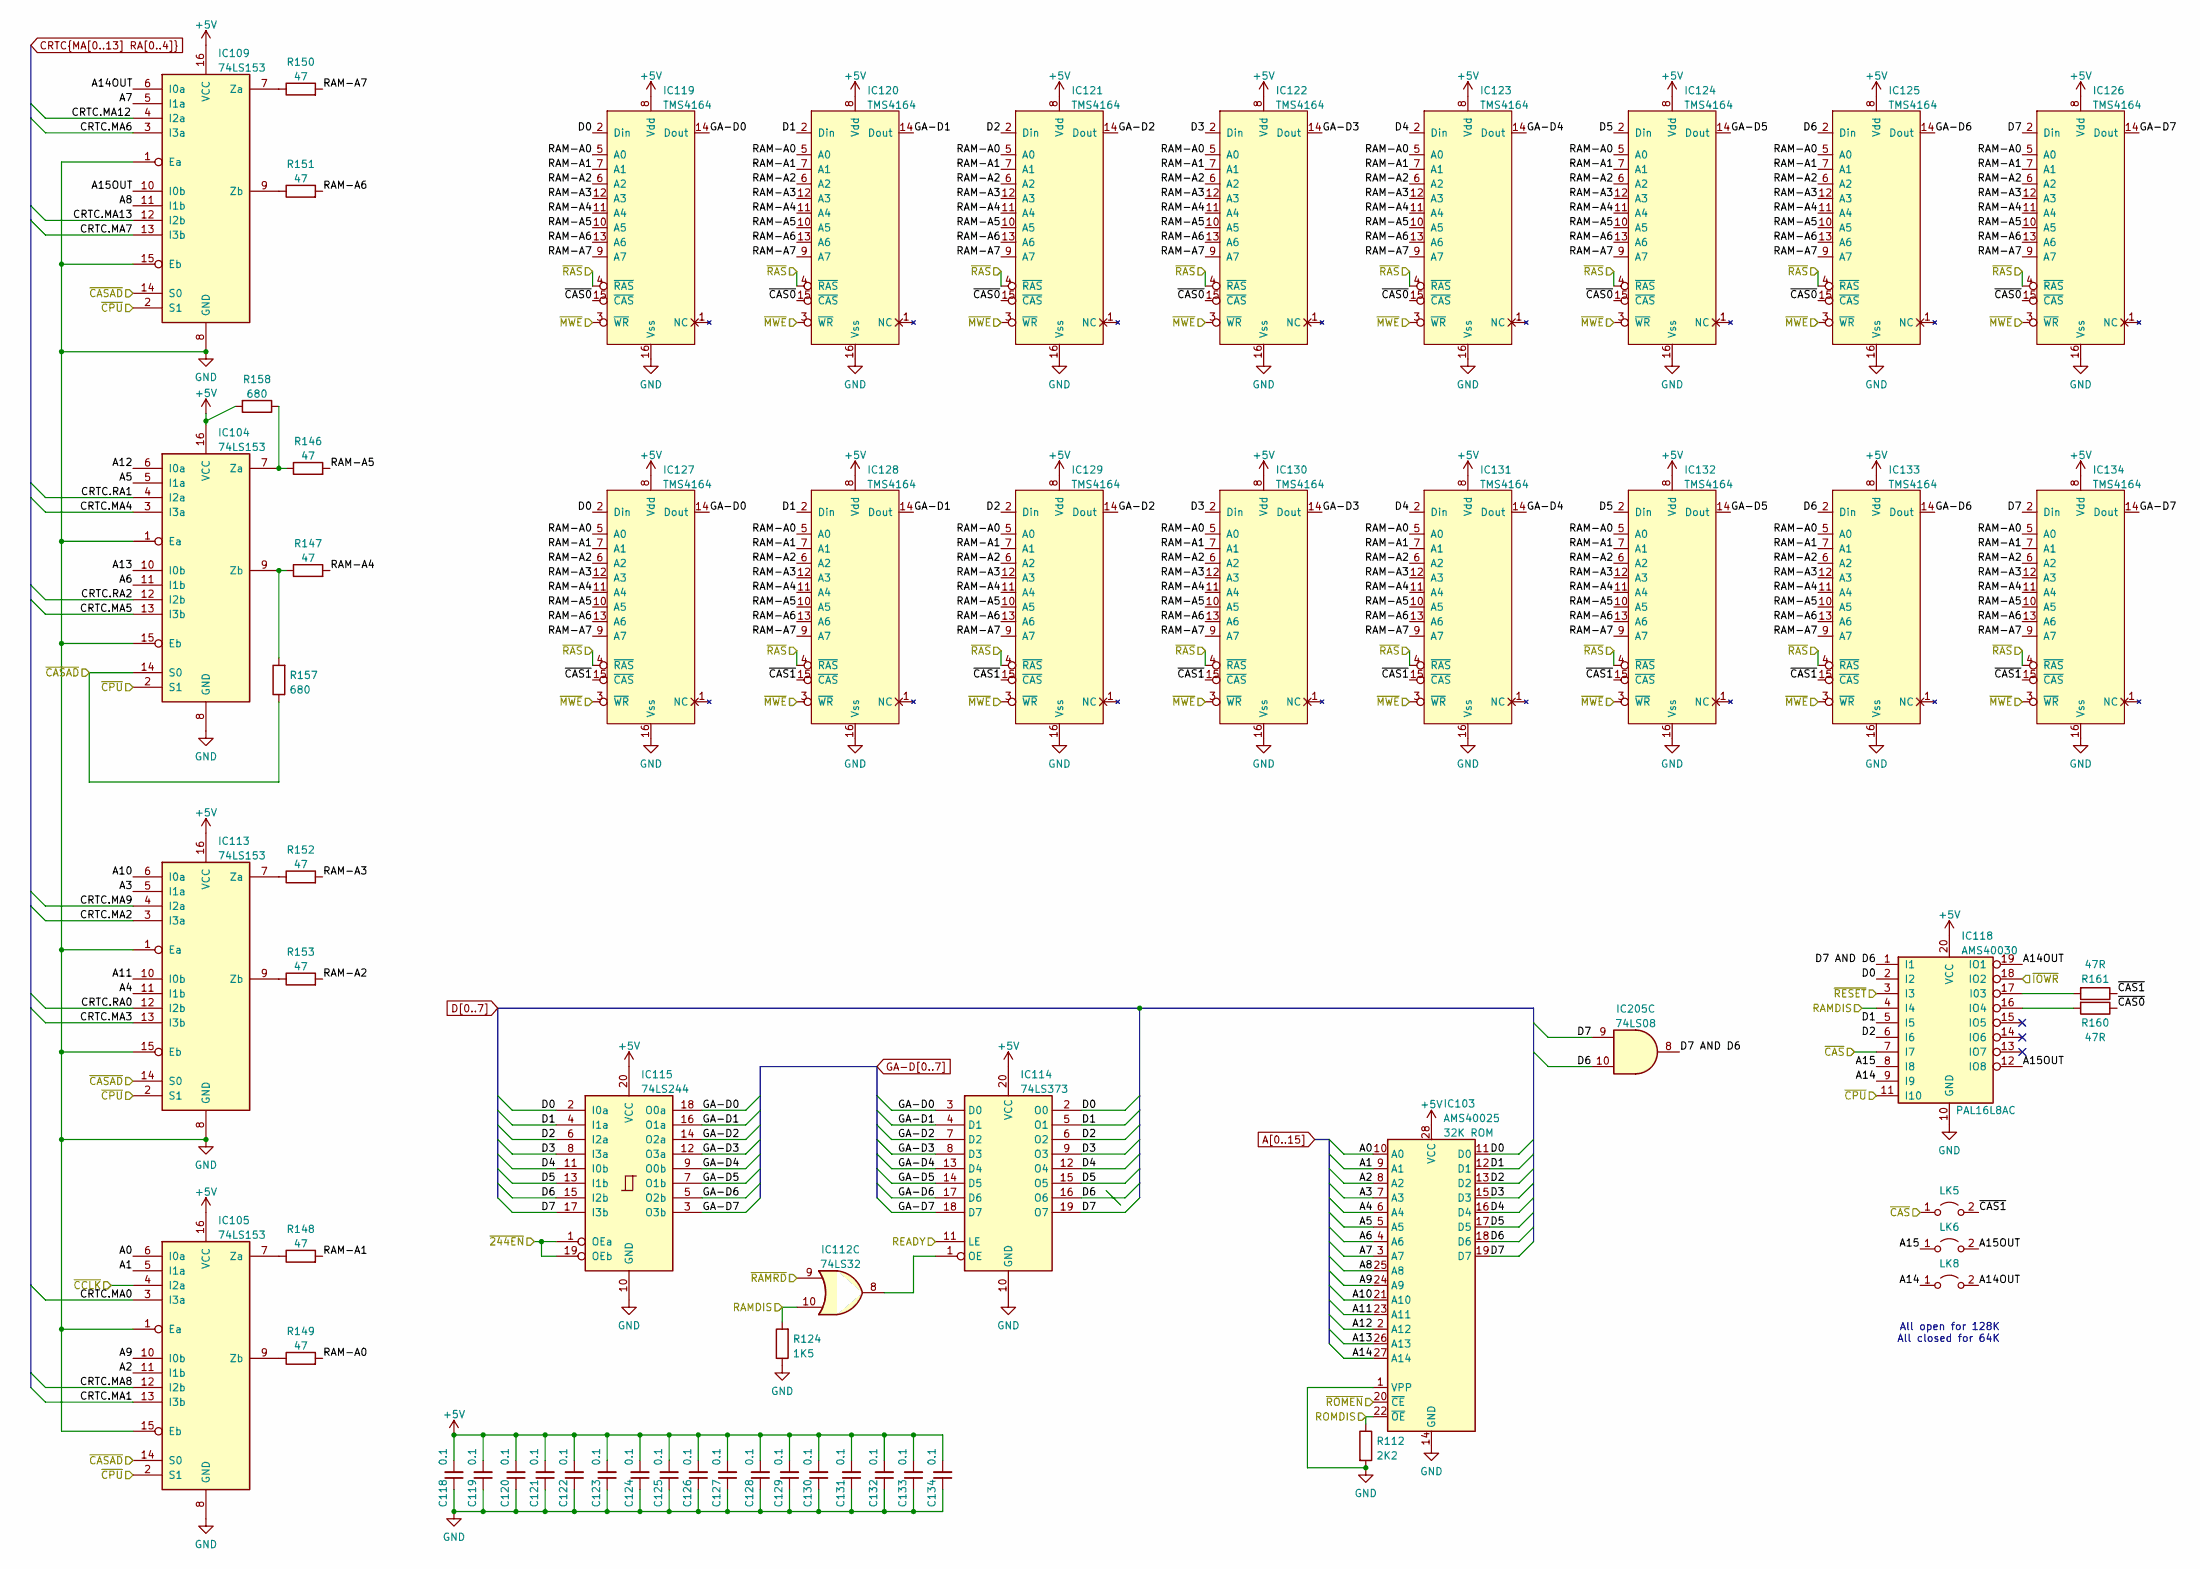
[picture p22: schematic memory.kicad_sch]

Parts:
C118, C119, C120, C121, C122, C123, C124, C125, C126, C127, C128, C129, C130, C131, C132, C133, C134: 0.1; C_Disc_D4.3mm_W1.9mm_P5.00mm
IC103: AMS40025; DIP-28_W15.24mm
IC104, IC105, IC109, IC113: 74LS153; DIP-16_W7.62mm
IC112: 74LS32; DIP-14_W7.62mm
IC114: 74LS373; DIP-20_W7.62mm
IC115: 74LS244; DIP-20_W7.62mm
IC118: AMS40030; DIP-20_W7.62mm_Socket
IC119, IC120, IC121, IC122, IC123, IC124, IC125, IC126, IC127, IC128, IC129, IC130, IC131, IC132, IC133, IC134: TMS4164; DIP-16_W7.62mm
IC205: 74LS08; DIP-14_W7.62mm
LK5, LK6, LK8: Jumper_2_Open; LINK
R112: 2K2; R_Axial_DIN0207_L6.3mm_D2.5mm_P10.16mm_Horizontal
R124: 1K5; R_Axial_DIN0207_L6.3mm_D2.5mm_P10.16mm_Horizontal
R146, R147, R148, R149, R150, R151, R152, R153: 47; R_Axial_DIN0207_L6.3mm_D2.5mm_P10.16mm_Horizontal
R157, R158: 680; R_Axial_DIN0207_L6.3mm_D2.5mm_P10.16mm_Horizontal
R160, R161: 47R; R_Axial_DIN0207_L6.3mm_D2.5mm_P10.16mm_Horizontal

Connections:
+5V: C118.2, C119.2, C120.2, C121.2, C122.2, C123.2, C124.2, C125.2, C126.2, C127.2, C128.2, C129.2, C130.2, C131.2, C132.2, C133.2, C134.2, IC103.28 (VCC), IC104.16 (VCC), IC105.16 (VCC), IC109.16 (VCC), IC113.16 (VCC), IC114.20 (VCC), IC115.20 (VCC), IC118.20 (VCC), IC119.8 (Vdd), IC120.8 (Vdd), IC121.8 (Vdd), IC122.8 (Vdd), IC123.8 (Vdd), IC124.8 (Vdd), IC125.8 (Vdd), IC126.8 (Vdd), IC127.8 (Vdd), IC128.8 (Vdd), IC129.8 (Vdd), IC130.8 (Vdd), IC131.8 (Vdd), IC132.8 (Vdd), IC133.8 (Vdd), IC134.8 (Vdd), R158.2
A0: IC103.10 (A0), IC105.6 (I0a)
A1: IC103.9 (A1), IC105.5 (I1a)
A2: IC103.8 (A2), IC105.11 (I1b)
A3: IC103.7 (A3), IC113.5 (I1a)
A4: IC103.6 (A4), IC113.11 (I1b)
A5: IC103.5 (A5), IC104.5 (I1a)
A6: IC103.4 (A6), IC104.11 (I1b)
A7: IC103.3 (A7), IC109.5 (I1a)
A8: IC103.25 (A8), IC109.11 (I1b)
A9: IC103.24 (A9), IC105.10 (I0b)
A10: IC103.21 (A10), IC113.6 (I0a)
A11: IC103.23 (A11), IC113.10 (I0b)
A12: IC103.2 (A12), IC104.6 (I0a)
A13: IC103.26 (A13), IC104.10 (I0b)
A14: IC103.27 (A14), IC118.9 (I9), LK8.1 (A)
A14OUT: IC109.6 (I0a), IC118.19 (IO1), LK8.2 (B)
A15: IC118.8 (I8), LK6.1 (A)
A15OUT: IC109.10 (I0b), IC118.12 (IO8), LK6.2 (B)
CRTC.MA0: IC105.3 (I3a)
CRTC.MA1: IC105.13 (I3b)
CRTC.MA2: IC113.3 (I3a)
CRTC.MA3: IC113.13 (I3b)
CRTC.MA4: IC104.3 (I3a)
CRTC.MA5: IC104.13 (I3b)
CRTC.MA6: IC109.3 (I3a)
CRTC.MA7: IC109.13 (I3b)
CRTC.MA8: IC105.12 (I2b)
CRTC.MA9: IC113.4 (I2a)
CRTC.MA12: IC109.4 (I2a)
CRTC.MA13: IC109.12 (I2b)
CRTC.RA0: IC113.12 (I2b)
CRTC.RA1: IC104.4 (I2a)
CRTC.RA2: IC104.12 (I2b)
D0: IC103.11 (D0), IC114.2 (O0), IC115.2 (I0a), IC118.2 (I2), IC119.2 (Din), IC127.2 (Din)
D1: IC103.12 (D1), IC114.5 (O1), IC115.4 (I1a), IC118.5 (I5), IC120.2 (Din), IC128.2 (Din)
D2: IC103.13 (D2), IC114.6 (O2), IC115.6 (I2a), IC118.6 (I6), IC121.2 (Din), IC129.2 (Din)
D3: IC103.15 (D3), IC114.9 (O3), IC115.8 (I3a), IC122.2 (Din), IC130.2 (Din)
D4: IC103.16 (D4), IC114.12 (O4), IC115.11 (I0b), IC123.2 (Din), IC131.2 (Din)
D5: IC103.17 (D5), IC114.15 (O5), IC115.13 (I1b), IC124.2 (Din), IC132.2 (Din)
D6: IC103.18 (D6), IC114.16 (O6), IC115.15 (I2b), IC125.2 (Din), IC133.2 (Din), IC205.10
D7: IC103.19 (D7), IC114.19 (O7), IC115.17 (I3b), IC126.2 (Din), IC134.2 (Din), IC205.9
D7 AND D6: IC118.1 (I1), IC205.8
GA-D0: IC114.3 (D0), IC115.18 (O0a), IC119.14 (Dout), IC127.14 (Dout)
GA-D1: IC114.4 (D1), IC115.16 (O1a), IC120.14 (Dout), IC128.14 (Dout)
GA-D2: IC114.7 (D2), IC115.14 (O2a), IC121.14 (Dout), IC129.14 (Dout)
GA-D3: IC114.8 (D3), IC115.12 (O3a), IC122.14 (Dout), IC130.14 (Dout)
GA-D4: IC114.13 (D4), IC115.9 (O0b), IC123.14 (Dout), IC131.14 (Dout)
GA-D5: IC114.14 (D5), IC115.7 (O1b), IC124.14 (Dout), IC132.14 (Dout)
GA-D6: IC114.17 (D6), IC115.5 (O2b), IC125.14 (Dout), IC133.14 (Dout)
GA-D7: IC114.18 (D7), IC115.3 (O3b), IC126.14 (Dout), IC134.14 (Dout)
GND: C118.1, C119.1, C120.1, C121.1, C122.1, C123.1, C124.1, C125.1, C126.1, C127.1, C128.1, C129.1, C130.1, C131.1, C132.1, C133.1, C134.1, IC103.1 (VPP), IC103.14 (GND), IC104.1 (Ea), IC104.8 (GND), IC104.15 (Eb), IC105.1 (Ea), IC105.8 (GND), IC105.15 (Eb), IC109.1 (Ea), IC109.8 (GND), IC109.15 (Eb), IC113.1 (Ea), IC113.8 (GND), IC113.15 (Eb), IC114.10 (GND), IC115.10 (GND), IC118.10 (GND), IC119.16 (Vss), IC120.16 (Vss), IC121.16 (Vss), IC122.16 (Vss), IC123.16 (Vss), IC124.16 (Vss), IC125.16 (Vss), IC126.16 (Vss), IC127.16 (Vss), IC128.16 (Vss), IC129.16 (Vss), IC130.16 (Vss), IC131.16 (Vss), IC132.16 (Vss), IC133.16 (Vss), IC134.16 (Vss), R112.2, R124.1
unnamed: IC104.7 (Za), R146.1, R158.1
unnamed: IC104.9 (Zb), R147.1, R157.2
unnamed: IC105.7 (Za), R148.1
unnamed: IC105.9 (Zb), R149.1
unnamed: IC109.7 (Za), R150.1
unnamed: IC109.9 (Zb), R151.1
unnamed: IC112.8, IC114.1 (OE)
unnamed: IC113.7 (Za), R152.1
unnamed: IC113.9 (Zb), R153.1
unnamed: IC118.16 (IO4), R160.2
unnamed: IC118.17 (I03), R161.2
RAM-A0: IC119.5 (A0), IC120.5 (A0), IC121.5 (A0), IC122.5 (A0), IC123.5 (A0), IC124.5 (A0), IC125.5 (A0), IC126.5 (A0), IC127.5 (A0), IC128.5 (A0), IC129.5 (A0), IC130.5 (A0), IC131.5 (A0), IC132.5 (A0), IC133.5 (A0), IC134.5 (A0), R149.2
RAM-A1: IC119.7 (A1), IC120.7 (A1), IC121.7 (A1), IC122.7 (A1), IC123.7 (A1), IC124.7 (A1), IC125.7 (A1), IC126.7 (A1), IC127.7 (A1), IC128.7 (A1), IC129.7 (A1), IC130.7 (A1), IC131.7 (A1), IC132.7 (A1), IC133.7 (A1), IC134.7 (A1), R148.2
RAM-A2: IC119.6 (A2), IC120.6 (A2), IC121.6 (A2), IC122.6 (A2), IC123.6 (A2), IC124.6 (A2), IC125.6 (A2), IC126.6 (A2), IC127.6 (A2), IC128.6 (A2), IC129.6 (A2), IC130.6 (A2), IC131.6 (A2), IC132.6 (A2), IC133.6 (A2), IC134.6 (A2), R153.2
RAM-A3: IC119.12 (A3), IC120.12 (A3), IC121.12 (A3), IC122.12 (A3), IC123.12 (A3), IC124.12 (A3), IC125.12 (A3), IC126.12 (A3), IC127.12 (A3), IC128.12 (A3), IC129.12 (A3), IC130.12 (A3), IC131.12 (A3), IC132.12 (A3), IC133.12 (A3), IC134.12 (A3), R152.2
RAM-A4: IC119.11 (A4), IC120.11 (A4), IC121.11 (A4), IC122.11 (A4), IC123.11 (A4), IC124.11 (A4), IC125.11 (A4), IC126.11 (A4), IC127.11 (A4), IC128.11 (A4), IC129.11 (A4), IC130.11 (A4), IC131.11 (A4), IC132.11 (A4), IC133.11 (A4), IC134.11 (A4), R147.2
RAM-A5: IC119.10 (A5), IC120.10 (A5), IC121.10 (A5), IC122.10 (A5), IC123.10 (A5), IC124.10 (A5), IC125.10 (A5), IC126.10 (A5), IC127.10 (A5), IC128.10 (A5), IC129.10 (A5), IC130.10 (A5), IC131.10 (A5), IC132.10 (A5), IC133.10 (A5), IC134.10 (A5), R146.2
RAM-A6: IC119.13 (A6), IC120.13 (A6), IC121.13 (A6), IC122.13 (A6), IC123.13 (A6), IC124.13 (A6), IC125.13 (A6), IC126.13 (A6), IC127.13 (A6), IC128.13 (A6), IC129.13 (A6), IC130.13 (A6), IC131.13 (A6), IC132.13 (A6), IC133.13 (A6), IC134.13 (A6), R151.2
RAM-A7: IC119.9 (A7), IC120.9 (A7), IC121.9 (A7), IC122.9 (A7), IC123.9 (A7), IC124.9 (A7), IC125.9 (A7), IC126.9 (A7), IC127.9 (A7), IC128.9 (A7), IC129.9 (A7), IC130.9 (A7), IC131.9 (A7), IC132.9 (A7), IC133.9 (A7), IC134.9 (A7), R150.2
RAMDIS: IC112.10, IC118.4 (I4), R124.2
READY: IC114.11 (LE)
ROMDIS: IC103.22 (~OE), R112.1
~244EN: IC115.1 (OEa), IC115.19 (OEb)
~CAS0: IC119.15 (~CAS), IC120.15 (~CAS), IC121.15 (~CAS), IC122.15 (~CAS), IC123.15 (~CAS), IC124.15 (~CAS), IC125.15 (~CAS), IC126.15 (~CAS), R160.1
~CAS1: IC127.15 (~CAS), IC128.15 (~CAS), IC129.15 (~CAS), IC130.15 (~CAS), IC131.15 (~CAS), IC132.15 (~CAS), IC133.15 (~CAS), IC134.15 (~CAS), LK5.2 (B), R161.1
~CASAD: IC104.14 (S0), IC105.14 (S0), IC109.14 (S0), IC113.14 (S0), R157.1
~CAS: IC118.7 (I7), LK5.1 (A)
~CCLK: IC105.4 (I2a)
~CPU: IC104.2 (S1), IC105.2 (S1), IC109.2 (S1), IC113.2 (S1), IC118.11 (I10)
~IOWR: IC118.18 (IO2)
~MWE: IC119.3 (~WR), IC120.3 (~WR), IC121.3 (~WR), IC122.3 (~WR), IC123.3 (~WR), IC124.3 (~WR), IC125.3 (~WR), IC126.3 (~WR), IC127.3 (~WR), IC128.3 (~WR), IC129.3 (~WR), IC130.3 (~WR), IC131.3 (~WR), IC132.3 (~WR), IC133.3 (~WR), IC134.3 (~WR)
~RAMRD: IC112.9
~RAS: IC119.4 (~RAS), IC120.4 (~RAS), IC121.4 (~RAS), IC122.4 (~RAS), IC123.4 (~RAS), IC124.4 (~RAS), IC125.4 (~RAS), IC126.4 (~RAS), IC127.4 (~RAS), IC128.4 (~RAS), IC129.4 (~RAS), IC130.4 (~RAS), IC131.4 (~RAS), IC132.4 (~RAS), IC133.4 (~RAS), IC134.4 (~RAS)
~RESET: IC118.3 (I3)
~ROMEN: IC103.20 (~CE)

Notes on the sheet:
All open for 128K All closed for 64K
