pelrun/cpc-schematics/cpc6128/tape.kicad_sch

## KiCad design cpc6128/tape.kicad_sch (2025-07-12)

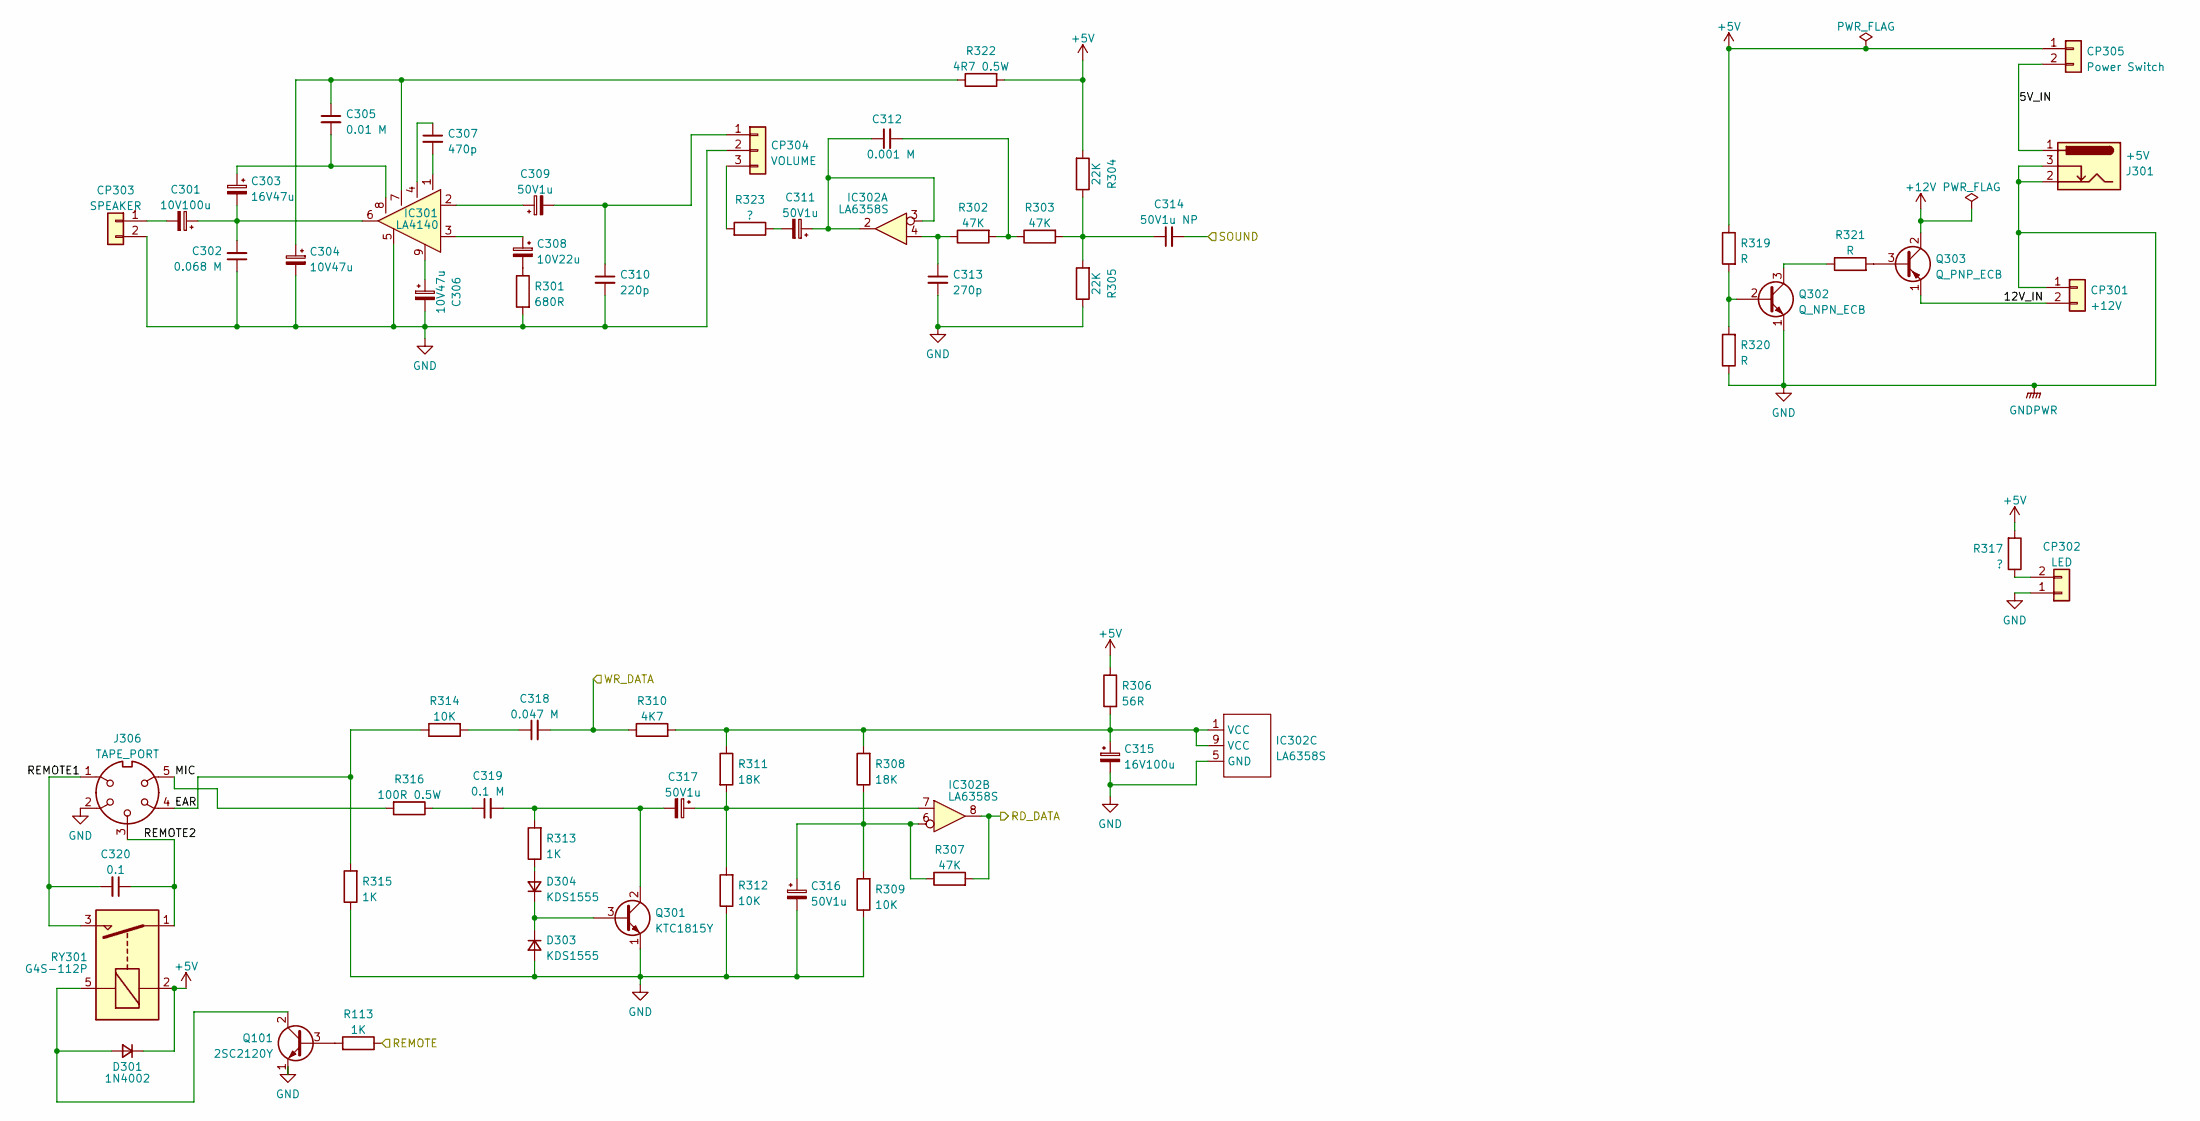
[picture p23: schematic tape.kicad_sch]

Parts:
C301: 10V100u; CP_Radial_D4.0mm_P5.00mm
C302: 0.068 M; C_Rect_L7.0mm_W2.0mm_P5.00mm
C303: 16V47u; CP_Radial_D4.0mm_P5.00mm
C304, C306: 10V47u; CP_Radial_D4.0mm_P5.00mm
C305: 0.01 M; C_Rect_L7.0mm_W2.0mm_P5.00mm
C307: 470p; C_Disc_D4.3mm_W1.9mm_P5.00mm
C308: 10V22u; CP_Radial_D4.0mm_P5.00mm
C309, C311, C316, C317: 50V1u; CP_Radial_D4.0mm_P5.00mm
C310: 220p; C_Disc_D4.3mm_W1.9mm_P5.00mm
C312: 0.001 M; C_Rect_L7.0mm_W2.0mm_P5.00mm
C313: 270p; C_Disc_D4.3mm_W1.9mm_P5.00mm
C314: 50V1u NP; C_Radial_D4.0mm_P5.00mm
C315: 16V100u; CP_Radial_D4.0mm_P5.00mm
C318: 0.047 M; C_Rect_L7.0mm_W2.0mm_P5.00mm
C319: 0.1 M; C_Rect_L7.0mm_W2.0mm_P5.00mm
C320: 0.1; C_Disc_D4.3mm_W1.9mm_P5.00mm
CP301: +12V; Molex_KK-254_AE-6410-02A_1x02_P2.54mm_Vertical
CP302: LED; Molex_KK-254_AE-6410-02A_1x02_P2.54mm_Vertical
CP303: SPEAKER; Molex_KK-254_AE-6410-02A_1x02_P2.54mm_Vertical
CP304: VOLUME; Molex_KK-254_AE-6410-03A_1x03_P2.54mm_Vertical
CP305: Power Switch; Molex_KK-254_AE-6410-02A_1x02_P2.54mm_Vertical
D301: 1N4002; D_DO-35_SOD27_P10.16mm_Horizontal
D303, D304: KDS1555; D_DO-35_SOD27_P10.16mm_Horizontal
IC301: LA4140; SIP-9_22.3x3mm_P2.54mm
IC302: LA6358S; SIP-9_22.3x3mm_P2.54mm
J301: +5V; BarrelJack_Wuerth_6941xx301002
J306: TAPE_PORT; TCS4450
Q101: 2SC2120Y; TO-92_Inline_Wide
Q301: KTC1815Y; TO-92_Inline_Wide
Q302: Q_NPN_ECB; TO-92_Inline_Wide
Q303: Q_PNP_ECB; TO-92_Inline_Wide
R113, R313, R315: 1K; R_Axial_DIN0207_L6.3mm_D2.5mm_P10.16mm_Horizontal
R301: 680R; R_Axial_DIN0207_L6.3mm_D2.5mm_P10.16mm_Horizontal
R302, R303, R307: 47K; R_Axial_DIN0207_L6.3mm_D2.5mm_P10.16mm_Horizontal
R304, R305: 22K; R_Axial_DIN0207_L6.3mm_D2.5mm_P10.16mm_Horizontal
R306: 56R; R_Axial_DIN0207_L6.3mm_D2.5mm_P10.16mm_Horizontal
R308, R311: 18K; R_Axial_DIN0207_L6.3mm_D2.5mm_P10.16mm_Horizontal
R309, R312, R314: 10K; R_Axial_DIN0207_L6.3mm_D2.5mm_P10.16mm_Horizontal
R310: 4K7; R_Axial_DIN0207_L6.3mm_D2.5mm_P10.16mm_Horizontal
R316: 100R 0.5W; R_Axial_DIN0207_L6.3mm_D2.5mm_P10.16mm_Horizontal
R317, R323: ?; R_Axial_DIN0207_L6.3mm_D2.5mm_P10.16mm_Horizontal
R319, R320, R321: R; R_Axial_DIN0207_L6.3mm_D2.5mm_P10.16mm_Horizontal
R322: 4R7 0.5W; R_Axial_DIN0207_L6.3mm_D2.5mm_P10.16mm_Horizontal
RY301: G4S-112P; Relay_SPST_SANYOU_SRD_Series_Form_A

Connections:
5V_IN: CP305.2, J301.1
12V_IN: CP301.2, Q303.1 (E)
+5V: CP305.1, D301.1 (K), R304.2, R306.1, R317.2, R319.1, R322.2, RY301.2
+12V: Q303.2 (C)
EAR: J306.4, R314.1, R315.2
GND: C302.1, C304.2, C306.2, C310.2, C313.2, C315.2, C316.2, CP301.1, CP302.1, CP303.2, CP304.2, D303.2 (A), IC301.5, IC302.5 (GND), J301.2, J301.3, J306.2, Q101.1 (E), Q301.1 (E), Q302.1 (E), R301.2, R305.1, R309.1, R312.1, R315.1, R320.1
MIC: J306.5, R316.2
unnamed: C301.1, C302.2, C303.2, IC301.6
unnamed: C301.2, CP303.1
unnamed: C303.1, C305.2, IC301.8
unnamed: C304.1, C305.1, IC301.7, R322.1
unnamed: C306.1, IC301.9
unnamed: C307.1, IC301.4
unnamed: C307.2, IC301.1
unnamed: C308.1, IC301.3
unnamed: C308.2, R301.1
unnamed: C309.1, IC301.2
unnamed: C309.2, C310.1, CP304.1
unnamed: C311.1, C312.1, IC302.2, IC302.3
unnamed: C311.2, R323.1
unnamed: C312.2, R302.2, R303.1
unnamed: C313.1, IC302.4, R302.1
unnamed: C314.1, R303.2, R304.1, R305.2
unnamed: C315.1, IC302.1 (VCC), IC302.9 (VCC), R306.2, R308.2, R310.2, R311.1
unnamed: C316.1, IC302.6, R307.1, R308.1, R309.2
unnamed: C317.1, IC302.7, R311.2, R312.2
unnamed: C317.2, C319.2, Q301.2 (C), R313.2
unnamed: C318.1, R314.2
unnamed: C319.1, R316.1
unnamed: CP302.2, R317.1
unnamed: CP304.3, R323.2
unnamed: D301.2 (A), Q101.2 (C), RY301.5
unnamed: D303.1 (K), D304.1 (K), Q301.3 (B)
unnamed: D304.2 (A), R313.1
unnamed: Q101.3 (B), R113.2
unnamed: Q302.2 (B), R319.2, R320.2
unnamed: Q302.3 (C), R321.1
unnamed: Q303.3 (B), R321.2
RD_DATA: IC302.8, R307.2
REMOTE: R113.1
REMOTE1: C320.2, J306.1, RY301.3
REMOTE2: C320.1, J306.3, RY301.1
SOUND: C314.2
WR_DATA: C318.2, R310.1
