pelrun/cpc-schematics/cpc6128/video.kicad_sch

## KiCad design cpc6128/video.kicad_sch (2025-07-12)

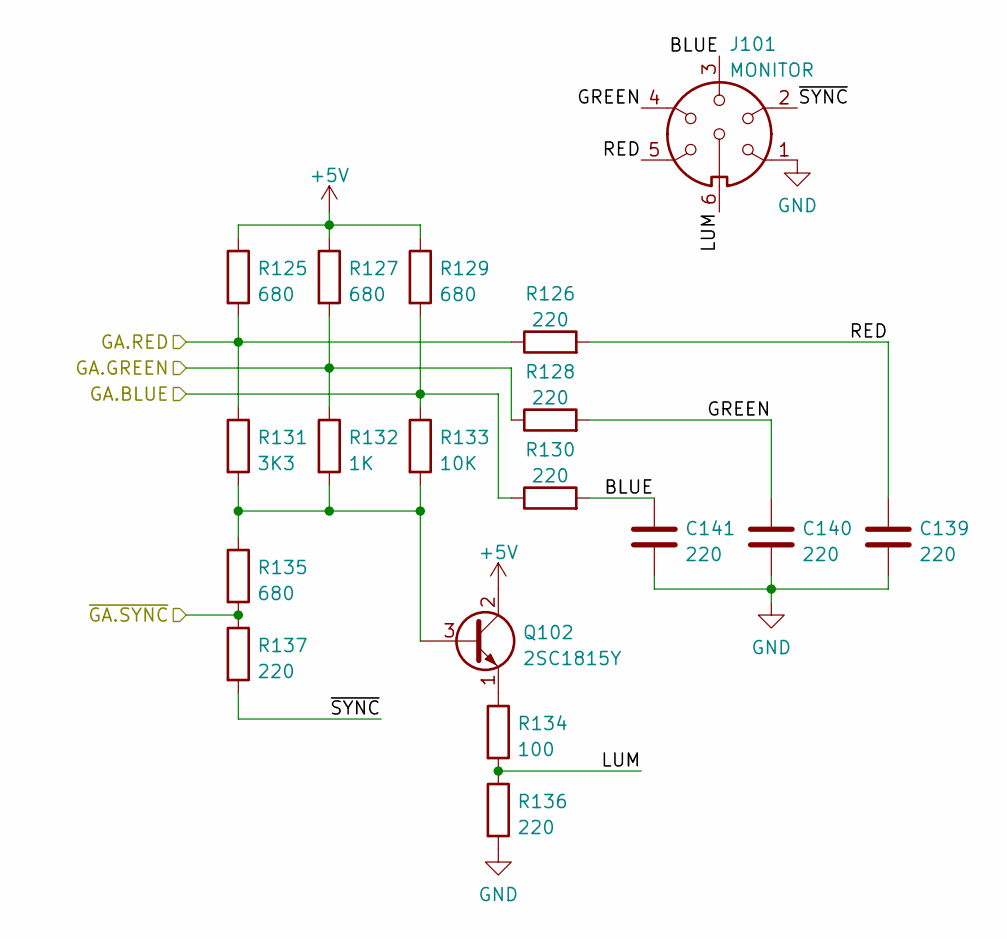
[picture p24: schematic video.kicad_sch]

Parts:
C139, C140, C141: 220; C_Disc_D4.3mm_W1.9mm_P5.00mm
J101: MONITOR; TCS4460
Q102: 2SC1815Y; TO-92_Inline_Wide
R125, R127, R129, R135: 680; R_Axial_DIN0207_L6.3mm_D2.5mm_P10.16mm_Horizontal
R126, R128, R130, R136, R137: 220; R_Axial_DIN0207_L6.3mm_D2.5mm_P10.16mm_Horizontal
R131: 3K3; R_Axial_DIN0207_L6.3mm_D2.5mm_P10.16mm_Horizontal
R132: 1K; R_Axial_DIN0207_L6.3mm_D2.5mm_P10.16mm_Horizontal
R133: 10K; R_Axial_DIN0207_L6.3mm_D2.5mm_P10.16mm_Horizontal
R134: 100; R_Axial_DIN0207_L6.3mm_D2.5mm_P10.16mm_Horizontal

Connections:
+5V: Q102.2 (C), R125.1, R127.1, R129.1
BLUE: C141.1, J101.3, R130.2
GA.BLUE: R129.2, R130.1, R133.1
GA.GREEN: R127.2, R128.1, R132.1
GA.RED: R125.2, R126.1, R131.1
GND: C139.2, C140.2, C141.2, J101.1, R136.2
GREEN: C140.1, J101.4, R128.2
LUM: J101.6, R134.2, R136.1
unnamed: Q102.1 (E), R134.1
unnamed: Q102.3 (B), R131.2, R132.2, R133.2, R135.1
RED: C139.1, J101.5, R126.2
~GA.SYNC: R135.2, R137.1
~SYNC: J101.2, R137.2
